abw/LED-Matrix/arduino/LED-Demo1/Waveforms.hpp

//---------------------------------------------------------------------
// Waveforms.hpp
//
// Header file containing function prototypes for waveform generator
// functions.
//
// Written by Andy Wardley <abw@wardley.org> February 2018
//---------------------------------------------------------------------

#ifndef WAVEFORMS_HPP
#define WAVEFORMS_HPP

double sinWave(double theta);
double squareWave(double theta);
double rampUpWave(double theta);
double rampDownWave(double theta);

#endif
